DerekSavage1/Word-Clock-Rev-3/Core/Src/Graphics/matrix.c

/*
 * matrix.c
 *
 *  Created on: Jan 22, 2024
 *      Author: dsava
 */
#include "matrix.h"
const uint16_t bitmap[][MATRIX_HEIGHT] = {
    //  1    2     3     4     5    6     7     8     9     10   11    12   13
    {   0,   0,    0,    0,    0,   0,    0,    0,    0,    7,   0,    0,   0}, // HOUR_ONE
    {   0,   0,    0,    0,    0,   0,    0,    0,    1792, 0,   0,    0,   0}, // HOUR_TWO
    {   0,   0,    0,    0,    0,   0,    0,    0,    0,    0,   496,  0,   0}, // HOUR_THREE
    {   0,   0,    0,    0,    0,   0,    0,    0,    15,   0,   0,    0,   0}, // HOUR_FOUR
    {   0,   0,    0,    0,    0,   0,    0,    0,    0,    0,   15,   0,   0}, // HOUR_FIVE
    {   0,   0,    0,    0,    0,   0,    1792, 0,    0,    0,   0,    0,   0}, // HOUR_SIX
    {   0,   0,    0,    0,    0,   0,    0,    248,  0,    0,   0,    0,   0}, // HOUR_SEVEN
    {   0,   0,    0,    0,    0,   0,    0,    0,    496,  0,   0,    0,   0}, // HOUR_EIGHT
    {   0,   0,    0,    0,    0,   0,    0,    0,    0,    1920,0,    0,   0}, // HOUR_NINE
    {   0,   0,    0,    0,    0,   0,    0,    7,    0,    0,   0,    0,   0}, // HOUR_TEN
    {   0,   0,    0,    0,    0,   0,    0,    0,    0,    252, 0,    0,   0}, // HOUR_ELEVEN
    {   0,   0,    0,    0,    0,   0,    0,    1920, 0,    0,   0,    0,   0}, // HOUR_NOON
    {   0,   0,    0,    0,    0,   0,    0,    0,    0,    0,   0,    2040,0}, // HOUR_MIDNIGHT
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
	{   0,   0,    0,    0,    0,   0,    0,    0,    0,    0,   0,    0,   256},// MENU_COLOR
	{   0,   0,    0,    0,    0,   0,    0,    0,    0,    0,   0,    0,   128},// MENU_BIRTHDAY
	{   0,   0,    0,    0,    0,   0,    0,    0,    0,    0,   0,    0,   64},// MENU_ANNIVERSARY

};
