DerekSavage1/Word-Clock-Rev-3/Core/Inc/constant.h

/*
 * constant.h
 *
 *  Created on: Apr 4, 2024
 *      Author: dsava
 */

#ifndef INC_CONSTANT_H_
#define INC_CONSTANT_H_


#include "main.h"
#include "WS2812B.h"
#include "display.h"

void constant(void);


#endif /* INC_CONSTANT_H_ */
