DerekSavage1/Word-Clock-Rev-3/Core/Inc/menu.h

/*
 * menu.h
 *
 *  Created on: Apr 2, 2024
 *      Author: dsava
 */

#ifndef INC_MENU_H_
#define INC_MENU_H_

#include <stdint.h>
#include "settings.h"
#include "blink.h"

void configureSettings(void);


#endif /* INC_MENU_H_ */
