DerekSavage1/Word-Clock-Rev-3/Core/Inc/twinkle.h

/*
 * twinkle.h
 *
 *  Created on: Apr 3, 2024
 *      Author: dsava
 */

#ifndef INC_TWINKLE_H_
#define INC_TWINKLE_H_

#include "WS2812B.h"
#include "random.h"
#include "display.h"
#include "settings.h"
#include "math.h"

void twinkle(void);

#endif /* INC_TWINKLE_H_ */
