DerekSavage1/Word-Clock-Rev-3/Core/Inc/button.h

/*
 * button.h
 *
 *  Created on: Apr 2, 2024
 *      Author: dsava
 */

#ifndef INC_BUTTON_H_
#define INC_BUTTON_H_

#include <settings.h>
#include <stdbool.h>
#include "main.h"


bool checkButtonPress(void);
void switchState();


#endif /* INC_BUTTON_H_ */
